compukidmike/Saintcon2021/Saintcon2021/ExternalFlash/crate.png

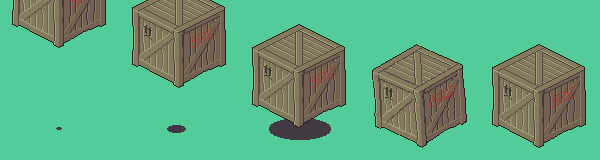
Saintcon2021/ExternalFlash/crate.png
