compukidmike/Saintcon2021/Saintcon2021/ExternalFlash/machine_bkg.png

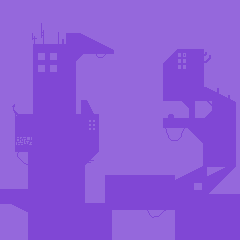
Saintcon2021/ExternalFlash/machine_bkg.png
