compukidmike/Saintcon2021/Saintcon2021/ExternalFlash/inventory.png

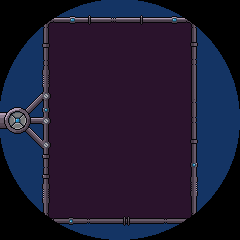
Saintcon2021/ExternalFlash/inventory.png
