compukidmike/Saintcon2021/Saintcon2021/ExternalFlash/build.png

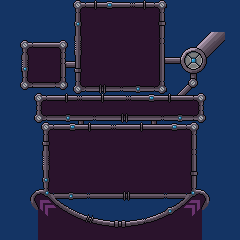
Saintcon2021/ExternalFlash/build.png
