compukidmike/Saintcon2021/Saintcon2021/Saintcon2021/atmel_start_pins.h

/*
 * Code generated from Atmel Start.
 *
 * This file will be overwritten when reconfiguring your Atmel Start project.
 * Please copy examples or other code you want to keep to a separate file
 * to avoid losing it when reconfiguring.
 */
#ifndef ATMEL_START_PINS_H_INCLUDED
#define ATMEL_START_PINS_H_INCLUDED

#include <hal_gpio.h>

// SAME53 has 14 pin functions

#define GPIO_PIN_FUNCTION_A 0
#define GPIO_PIN_FUNCTION_B 1
#define GPIO_PIN_FUNCTION_C 2
#define GPIO_PIN_FUNCTION_D 3
#define GPIO_PIN_FUNCTION_E 4
#define GPIO_PIN_FUNCTION_F 5
#define GPIO_PIN_FUNCTION_G 6
#define GPIO_PIN_FUNCTION_H 7
#define GPIO_PIN_FUNCTION_I 8
#define GPIO_PIN_FUNCTION_J 9
#define GPIO_PIN_FUNCTION_K 10
#define GPIO_PIN_FUNCTION_L 11
#define GPIO_PIN_FUNCTION_M 12
#define GPIO_PIN_FUNCTION_N 13

#define PA08 GPIO(GPIO_PORTA, 8)
#define PA09 GPIO(GPIO_PORTA, 9)
#define PA10 GPIO(GPIO_PORTA, 10)
#define PA11 GPIO(GPIO_PORTA, 11)
#define PA12 GPIO(GPIO_PORTA, 12)
#define PA13 GPIO(GPIO_PORTA, 13)
#define PA15 GPIO(GPIO_PORTA, 15)
#define PA16 GPIO(GPIO_PORTA, 16)
#define PA17 GPIO(GPIO_PORTA, 17)
#define PA18 GPIO(GPIO_PORTA, 18)
#define PA19 GPIO(GPIO_PORTA, 19)
#define PA20 GPIO(GPIO_PORTA, 20)
#define PA21 GPIO(GPIO_PORTA, 21)
#define PA22 GPIO(GPIO_PORTA, 22)
#define PA23 GPIO(GPIO_PORTA, 23)
#define PA24 GPIO(GPIO_PORTA, 24)
#define PA25 GPIO(GPIO_PORTA, 25)
#define PA27 GPIO(GPIO_PORTA, 27)
#define PB09 GPIO(GPIO_PORTB, 9)
#define PB10 GPIO(GPIO_PORTB, 10)
#define PB11 GPIO(GPIO_PORTB, 11)
#define PB12 GPIO(GPIO_PORTB, 12)
#define PB13 GPIO(GPIO_PORTB, 13)
#define PB14 GPIO(GPIO_PORTB, 14)
#define PB15 GPIO(GPIO_PORTB, 15)

#endif // ATMEL_START_PINS_H_INCLUDED
