compukidmike/Saintcon2021/Saintcon2021/Saintcon2021/small.c

#include <stdint.h>

// 'small', 160x80px
const uint16_t bird_raw [] = {
	0x5b2a, 0x5b4a, 0x634a, 0x636b, 0x6b8b, 0x6bab, 0x6bcc, 0x6bcc, 0x6bed, 0x6bed, 0x740e, 0x740d, 0x742e, 0x742e, 0x744e, 0x7c4e, 
	0x7c4e, 0x7c6f, 0x7c6f, 0x7c6f, 0x7c6f, 0x7c6f, 0x7c4f, 0x846f, 0x7c6f, 0x7c6f, 0x7c6f, 0x7c6f, 0x846f, 0x848f, 0x846f, 0x846f, 
	0x848f, 0x848f, 0x7c8f, 0x7c6f, 0x848f, 0x848f, 0x848f, 0x848f, 0x848f, 0x846f, 0x848f, 0x7c6f, 0x7c6f, 0x846f, 0x846f, 0x844f, 
	0x844f, 0x844f, 0x7c4e, 0x7c2e, 0x740d, 0x740d, 0x7c0d, 0x7c0d, 0x73ed, 0x73ed, 0x73cc, 0x73cc, 0x73ac, 0x738c, 0x738b, 0x6b8b, 
	0x6b6b, 0x6b6a, 0x6b4a, 0x634a, 0x6b6a, 0x634a, 0x634a, 0x6b4a, 0x6b4a, 0x6b29, 0x6329, 0x6b29, 0x6329, 0x6329, 0x6329, 0x6308, 
	0x6309, 0x6329, 0x6308, 0x5b28, 0x5b28, 0x5346, 0x5cc7, 0x5d26, 0x5d24, 0x3ce2, 0x34e1, 0x4d44, 0x3cc2, 0x3d23, 0x24e0, 0x24c0, 
	0x2502, 0x2ce2, 0x3d04, 0x2c82, 0x3cc5, 0x54a8, 0x74cb, 0x6c29, 0x6b69, 0x636a, 0x6baa, 0x6b8a, 0x73a9, 0x6b88, 0x6b87, 0x7388, 
	0x7367, 0x7387, 0x7366, 0x7365, 0x7345, 0x7346, 0x7345, 0x7344, 0x7345, 0x7345, 0x7365, 0x6b45, 0x7346, 0x7346, 0x6b27, 0x6b27, 
	0x6b07, 0x6b08, 0x6b08, 0x62e8, 0x62e8, 0x62e8, 0x62e9, 0x5ae9, 0x5ac9, 0x5ae9, 0x5ac9, 0x52c9, 0x52c9, 0x52a9, 0x52a9, 0x52a9, 
	0x52c9, 0x52c8, 0x5ac9, 0x5ae9, 0x5ae8, 0x5b08, 0x5b08, 0x6307, 0x6306, 0x6327, 0x6306, 0x6326, 0x6b26, 0x6b47, 0x7347, 0x7327, 
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
	0x6b09, 0x6309, 0x6309, 0x62e9, 0x62e9, 0x62e9, 0x5ae9, 0x5ae9, 0x5aea, 0x5ae9, 0x5aca, 0x52ca, 0x52a9, 0x52c9, 0x52c9, 0x52c8, 
	0x5ac8, 0x5aa8, 0x5ac8, 0x62e8, 0x6307, 0x6307, 0x6327, 0x6327, 0x6326, 0x6326, 0x6326, 0x6325, 0x6324, 0x6324, 0x6324, 0x6b25, 
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
};
