compukidmike/Saintcon2021/Saintcon2021/Saintcon2021/menu_icons.h

/*
 * menu_icons.h
 *
 * Created: 8/21/2021 8:44:59 PM
 *  Author: Professor Plum
 */ 

//
//  menu_icons.h
//  SC2021
//
//  Created by Professor Plum on 8/10/21.
//

#ifndef menu_icons_h
#define menu_icons_h

#include <stdint.h>

static const uint8_t menu_icons[7][128] = {
	{
		0x00, 0x00, 0x00, 0x00, 0x00, 0x00, 0x00, 0x00, 0x00, 0x00, 0x00, 0x00, 
  0x00, 0x00, 0x40, 0x00, 0x00, 0x00, 0xE0, 0x00, 0x00, 0x00, 0xE0, 0x00, 
  0x00, 0x00, 0xC0, 0x01, 0x00, 0x00, 0xC4, 0x03, 0x00, 0x00, 0x8E, 0x03, 
  0x00, 0x00, 0x0C, 0x03, 0x00, 0x40, 0x18, 0x07, 0x40, 0xE0, 0x38, 0x07, 
  0xE0, 0xE0, 0x39, 0x0F, 0xF0, 0xC3, 0x31, 0x0E, 0xF0, 0x87, 0x31, 0x0E, 
  0x70, 0x8F, 0x31, 0x0E, 0x70, 0x9E, 0x31, 0x0E, 0x60, 0xBC, 0x31, 0x0E, 
  0xE0, 0xF8, 0x31, 0x0E, 0xE0, 0xF0, 0x39, 0x0F, 0x40, 0xE0, 0x38, 0x07, 
  0x00, 0x40, 0x18, 0x07, 0x00, 0x00, 0x0C, 0x03, 0x00, 0x00, 0x8E, 0x03, 
  0x00, 0x00, 0xC4, 0x03, 0x00, 0x00, 0xC0, 0x01, 0x00, 0x00, 0xE0, 0x00, 
  0x00, 0x00, 0xE0, 0x00, 0x00, 0x00, 0x40, 0x00, 0x00, 0x00, 0x00, 0x00, 
  0x00, 0x00, 0x00, 0x00, 0x00, 0x00, 0x00, 0x00, 
	},
	{
		0x00, 0x00, 0x00, 0x00, 0x00, 0x00, 0x00, 0x00, 0x00, 0x80, 0x01, 0x00, 
		0x00, 0x60, 0x06, 0x00, 0x00, 0x18, 0x1E, 0x00, 0x00, 0x86, 0x61, 0x00, 
		0x00, 0x7A, 0x78, 0x00, 0x00, 0x62, 0x7E, 0x00, 0x00, 0x82, 0x7F, 0x00, 
		0x00, 0x02, 0x7F, 0x00, 0x00, 0x02, 0x7F, 0x00, 0x00, 0x02, 0x7F, 0x00, 
		0x00, 0x06, 0x7F, 0x00, 0x00, 0x18, 0x1F, 0x00, 0x80, 0x61, 0x87, 0x01, 
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
		0xF0, 0x1F, 0x00, 0x00, 0xF8, 0x0F, 0x00, 0x00, 0xFC, 0x07, 0x00, 0x00, 
		0xFE, 0x07, 0x00, 0x00, 0xFC, 0x03, 0x00, 0x00, 0xF8, 0x01, 0x00, 0x00, 
		0xF0, 0x00, 0x00, 0x00, 0x60, 0x00, 0x00, 0x00, 0x00, 0x00, 0x00, 0x00, 
		0x00, 0x00, 0x00, 0x00, 0x00, 0x00, 0x00, 0x00,
	}
};

static const uint8_t no_icon[] = {
  0x00, 0xF0, 0x0F, 0x00, 0x00, 0xFE, 0x7F, 0x00, 0x00, 0xFF, 0xFF, 0x00, 
  0xC0, 0xFF, 0xFF, 0x03, 0xE0, 0x1F, 0xF8, 0x07, 0xF0, 0x03, 0xC0, 0x0F, 
  0xF8, 0x01, 0x80, 0x1F, 0xF8, 0x01, 0x00, 0x1E, 0xFC, 0x03, 0x00, 0x3E, 
  0xFE, 0x07, 0x00, 0x7C, 0x9E, 0x0F, 0x00, 0x78, 0x1E, 0x1F, 0x00, 0x78, 
  0x1F, 0x3E, 0x00, 0xF8, 0x0F, 0x7C, 0x00, 0xF0, 0x0F, 0xF8, 0x00, 0xF0, 
  0x0F, 0xF0, 0x01, 0xF0, 0x0F, 0xE0, 0x03, 0xF0, 0x0F, 0xC0, 0x07, 0xF0, 
  0x0F, 0x80, 0x0F, 0xF0, 0x1F, 0x00, 0x1F, 0xF8, 0x1E, 0x00, 0x3E, 0x78, 
  0x1E, 0x00, 0x7C, 0x78, 0x3E, 0x00, 0xF8, 0x7C, 0x7C, 0x00, 0xF0, 0x3F, 
  0x78, 0x00, 0xE0, 0x1F, 0xF8, 0x01, 0xC0, 0x1F, 0xF0, 0x03, 0xC0, 0x0F, 
  0xE0, 0x1F, 0xF8, 0x07, 0xC0, 0xFF, 0xFF, 0x03, 0x00, 0xFF, 0xFF, 0x00, 
  0x00, 0xFE, 0x7F, 0x00, 0x00, 0xF0, 0x0F, 0x00, };


#endif /* menu_icons_h */
