compukidmike/Saintcon2021/Saintcon2021/Saintcon2021/combonums.h

/*
 * combonums.h
 *
 * Created: 8/21/2021 9:00:56 PM
 *  Author: Professor Plum
 */ 


#ifndef COMBONUMS_H_
#define COMBONUMS_H_


#include <stdint.h>

static const uint8_t num_bits[8][128] = {
	{ //0
		0x00, 0x00, 0x00, 0x00, 0x00, 0x00, 0x00, 0x00, 0x00, 0x00, 0x00, 0x00,
		0x00, 0x00, 0x00, 0x00, 0x00, 0x00, 0x00, 0x00, 0x00, 0xC0, 0x03, 0x00,
		0x00, 0xF0, 0x07, 0x00, 0x00, 0x38, 0x0E, 0x00, 0x00, 0x18, 0x0C, 0x00,
		0x00, 0x1C, 0x1C, 0x00, 0x00, 0x0C, 0x18, 0x00, 0x00, 0x0C, 0x18, 0x00,
		0x00, 0x0C, 0x18, 0x00, 0x00, 0x0C, 0x18, 0x00, 0x00, 0x0C, 0x18, 0x00,
		0x00, 0x0C, 0x18, 0x00, 0x00, 0x0C, 0x18, 0x00, 0x00, 0x1C, 0x1C, 0x00,
		0x00, 0x18, 0x0C, 0x00, 0x00, 0x38, 0x0E, 0x00, 0x00, 0xF0, 0x07, 0x00,
		0x00, 0xE0, 0x03, 0x00, 0x00, 0x00, 0x00, 0x00, 0x00, 0x00, 0x00, 0x00,
		0x00, 0x00, 0x00, 0x00, 0x00, 0x00, 0x00, 0x00, 0x00, 0x00, 0x00, 0x00,
		0x00, 0x00, 0x00, 0x00, 0x00, 0x00, 0x00, 0x00, 0x00, 0x00, 0x00, 0x00,
		0x00, 0x00, 0x00, 0x00, 0x00, 0x00, 0x00, 0x00,
	},
	{ //5
		0x00, 0x00, 0x00, 0x00, 0x00, 0x00, 0x00, 0x00, 0x00, 0x00, 0x00, 0x00,
		0x00, 0x00, 0x00, 0x00, 0x00, 0x00, 0x00, 0x00, 0x00, 0xF0, 0x0F, 0x00,
		0x00, 0xF8, 0x0F, 0x00, 0x00, 0x18, 0x00, 0x00, 0x00, 0x18, 0x00, 0x00,
		0x00, 0x18, 0x00, 0x00, 0x00, 0x18, 0x00, 0x00, 0x00, 0xD8, 0x03, 0x00,
		0x00, 0xF8, 0x0F, 0x00, 0x00, 0x1C, 0x0C, 0x00, 0x00, 0x00, 0x18, 0x00,
		0x00, 0x00, 0x18, 0x00, 0x00, 0x00, 0x18, 0x00, 0x00, 0x00, 0x18, 0x00,
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
	0x00, 0x00, 0x00, 0x00, 0x00, 0x00, 0x00, 0x00, 0x00, 0x00, 0x00, 0x00,
	0x00, 0x00, 0x00, 0x00, 0x00, 0x00, 0x00, 0x00, 0x00, 0x00, 0x00, 0x00,
	0x00, 0x00, 0x00, 0x00, 0x00, 0x00
};


static const uint8_t arrow[] = {0x7F, 0x3E, 0x1C, 0x08};
	
#endif /* COMBONUMS_H_ */
