compukidmike/Saintcon2021/Saintcon2021/Saintcon2021/Scenes/inventoryScene.c

/*
 * inventoryScene.c
 *
 * Created: 8/21/2021 9:35:53 PM
 *  Author: Professor Plum
 */ 

#include <stdio.h>
#include "main.h"
#include "FrameBuffer.h"
#include "machine_common.h"
#include "flash.h"

Scene inventory_scene_loop(bool init) {
	if (back_event) {
		back_event=false;
		return MENU;
	}
	if (init) {
		canvas_drawImage_FromFlash(0,0, 240, 240, INVENTORY_IMG);
		char line[20];
		int y = 24;
		for (int i=0; i<12; ++i) {
			if (g_state.part_count[i]) {
				snprintf(line, 20, "%2dx    %s", g_state.part_count[i], part_names[i]);
				canvas_drawText(53, y, line, RGB(200,200,200));
				int px = (i % 4)*16;
				int py = (i / 4)*16;
				canvas_drawImage_FromFlash_pt(85, y, 16, 16, PARTS_IMG, px, py, 64, RGB(242, 170, 206));
				y+=16;
			}
		}
		canvas_blt();
	}
	return INVENTORY;
}
