compukidmike/Saintcon2021/Saintcon2021/Saintcon2021/atmel_start.h

#ifndef ATMEL_START_H_INCLUDED
#define ATMEL_START_H_INCLUDED

#ifdef __cplusplus
extern "C" {
#endif

#include "driver_init.h"
#include "usb_start.h"

#include "touch.h"

/**
 * Initializes MCU, drivers and middleware in the project
 **/
void atmel_start_init(void);

#ifdef __cplusplus
}
#endif
#endif
