compukidmike/Saintcon2021/Saintcon2021/Saintcon2021/examples/driver_examples.c

/*
 * Code generated from Atmel Start.
 *
 * This file will be overwritten when reconfiguring your Atmel Start project.
 * Please copy examples or other code you want to keep to a separate file
 * to avoid losing it when reconfiguring.
 */

#include "driver_examples.h"
#include "driver_init.h"
#include "utils.h"

static uint8_t aes_plain_text[16]
    = {0x6b, 0xc1, 0xbe, 0xe2, 0x2e, 0x40, 0x9f, 0x96, 0xe9, 0x3d, 0x7e, 0x11, 0x73, 0x93, 0x17, 0x2a};
static uint8_t aes_key[16]
    = {0x2b, 0x7e, 0x15, 0x16, 0x28, 0xae, 0xd2, 0xa6, 0xab, 0xf7, 0x15, 0x88, 0x09, 0xcf, 0x4f, 0x3c};
static uint8_t aes_cipher_text[16]
    = {0x3a, 0xd7, 0x7b, 0xb4, 0x0d, 0x7a, 0x36, 0x60, 0xa8, 0x9e, 0xca, 0xf3, 0x24, 0x66, 0xef, 0x97};
uint8_t aes_output[16] = {0x00};
/**
 * Example of using CRYPTOGRAPHY_0 to Encrypt/Decrypt datas.
 */
void CRYPTOGRAPHY_0_example(void)
{
	int32_t i;
	aes_sync_enable(&CRYPTOGRAPHY_0);
	aes_sync_set_encrypt_key(&CRYPTOGRAPHY_0, aes_key, AES_KEY_128);
	aes_sync_ecb_crypt(&CRYPTOGRAPHY_0, AES_ENCRYPT, aes_plain_text, aes_output);
	for (i = 0; i < 16; i++) {
		while (aes_output[i] != aes_cipher_text[i])
			;
	}
}

static void button_on_PB09_pressed(void)
{

}

static void button_on_PA27_pressed(void)
{
}

/**
 * Example of using EXTERNAL_IRQ_0
 */
void EXTERNAL_IRQ_0_example(void)
{

	ext_irq_register(PIN_PB09, button_on_PB09_pressed);
	ext_irq_register(PIN_PA27, button_on_PA27_pressed);
}

COMPILER_ALIGNED(128)
struct sha_context context;
COMPILER_PACK_RESET();

/**
 * Example of using HASH_ALGORITHM_0 to generate SHA digest message.
 */
void HASH_ALGORITHM_0_example(void)
{
	const uint8_t sha1_digest[]  = {0xA9, 0x99, 0x3E, 0x36, 0x47, 0x06, 0x81, 0x6A, 0xBA, 0x3E,
                                   0x25, 0x71, 0x78, 0x50, 0xC2, 0x6C, 0x9C, 0xD0, 0xD8, 0x9D};
	uint8_t       sha_output[20] = {0x00};
	int32_t       i;

	sha_sync_enable(&HASH_ALGORITHM_0);
	sha_sync_sha1_compute(&HASH_ALGORITHM_0, &context, "abc", 3, sha_output);
	for (i = 0; i < 20; i++) {
		while (sha_output[i] != sha1_digest[i])
			;
	}
}

/**
 * Example of using QUAD_SPI_0 to get N25Q256A status value,
 * and check bit 0 which indicate embedded operation is busy or not.
 */
void QUAD_SPI_0_example(void)
{
	uint8_t              status = 0xFF;
	struct _qspi_command cmd    = {
        .inst_frame.bits.inst_en  = 1,
        .inst_frame.bits.data_en  = 1,
        .inst_frame.bits.tfr_type = QSPI_READ_ACCESS,
        .instruction              = 0x05,
        .buf_len                  = 1,
        .rx_buf                   = &status,
    };

	qspi_sync_enable(&QUAD_SPI_0);
	while (status & (1 << 0)) {
		qspi_sync_serial_run_command(&QUAD_SPI_0, &cmd);
	}
	qspi_sync_deinit(&QUAD_SPI_0);
}

static struct timer_task Timer_task1, Timer_task2;
/**
 * Example of using Timer.
 */
static void Timer_task1_cb(const struct timer_task *const timer_task)
{
}

static void Timer_task2_cb(const struct timer_task *const timer_task)
{
}

void Timer_example(void)
{
	Timer_task1.interval = 100;
	Timer_task1.cb       = Timer_task1_cb;
	Timer_task1.mode     = TIMER_TASK_REPEAT;
	Timer_task2.interval = 200;
	Timer_task2.cb       = Timer_task2_cb;
	Timer_task2.mode     = TIMER_TASK_REPEAT;

	timer_add_task(&Timer, &Timer_task1);
	timer_add_task(&Timer, &Timer_task2);
	timer_start(&Timer);
}

void I2C_0_example(void)
{
	struct io_descriptor *I2C_0_io;

	i2c_m_sync_get_io_descriptor(&I2C_0, &I2C_0_io);
	i2c_m_sync_enable(&I2C_0);
	i2c_m_sync_set_slaveaddr(&I2C_0, 0x12, I2C_M_SEVEN);
	io_write(I2C_0_io, (uint8_t *)"Hello World!", 12);
}

/**
 * Example of using SPI_1 to write "Hello World" using the IO abstraction.
 */
static uint8_t example_SPI_1[12] = "Hello World!";

void SPI_1_example(void)
{
	struct io_descriptor *io;
	spi_m_sync_get_io_descriptor(&SPI_1, &io);

	spi_m_sync_enable(&SPI_1);
	io_write(io, example_SPI_1, 12);
}

/**
 * Example of using PWM_0.
 */
void PWM_0_example(void)
{
	pwm_set_parameters(&PWM_0, 10000, 5000);
	pwm_enable(&PWM_0);
}

/**
 * Example of using RAND_0 to generate waveform.
 */
void RAND_0_example(void)
{
	uint32_t random_n[4];
	rand_sync_enable(&RAND_0);
	random_n[0] = rand_sync_read32(&RAND_0);
	random_n[1] = rand_sync_read32(&RAND_0);
	rand_sync_read_buf32(&RAND_0, &random_n[2], 2);
	if (random_n[0] == random_n[1]) {
		/* halt */
		while (1)
			;
	}
	if (random_n[2] == random_n[3]) {
		/* halt */
		while (1)
			;
	}
}
